dj1yr/Yaesu-Quadra-VL-1000-FAN-Controller/IMG_20241115_044554092.jpg

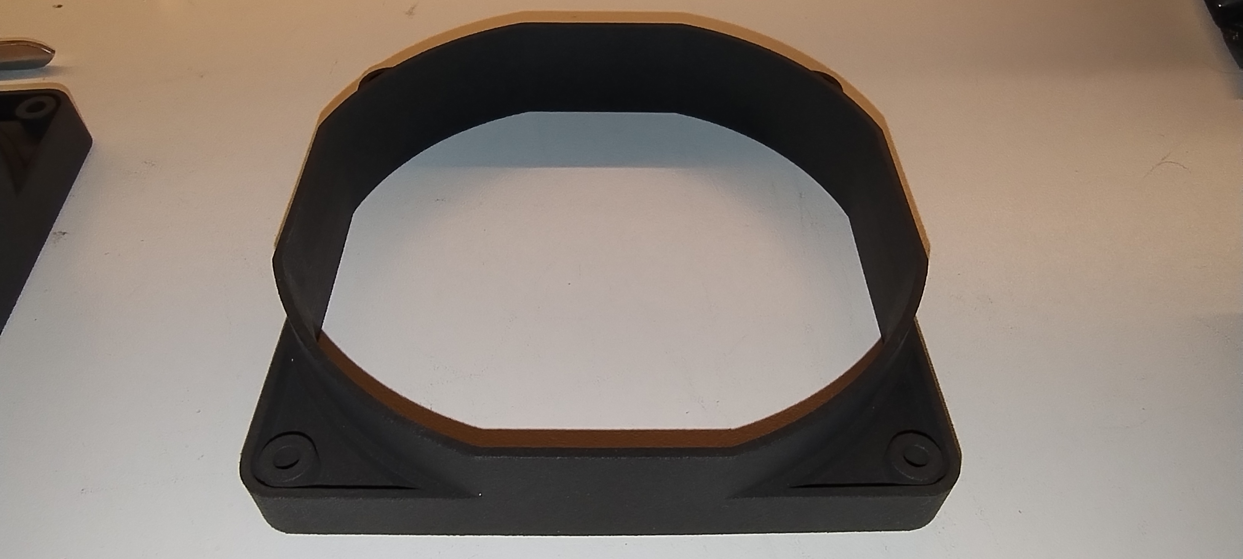
IMG_20241115_044554092.jpg
