dj1yr/Yaesu-Quadra-VL-1000-FAN-Controller/IMG_20241115_045349877.jpg

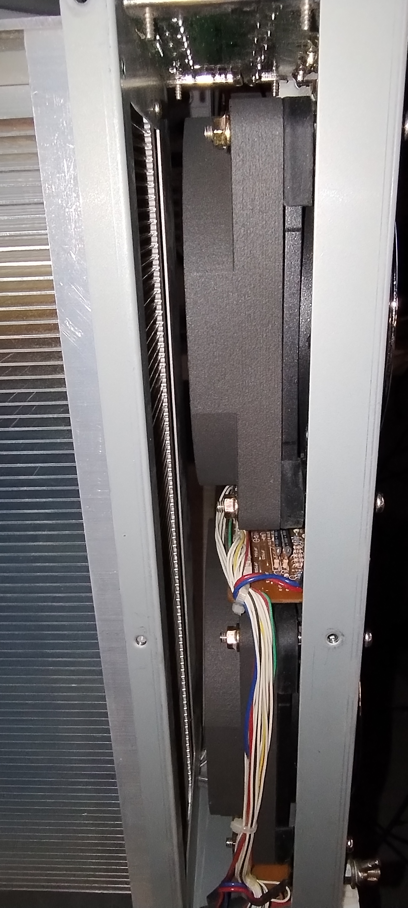
IMG_20241115_045349877.jpg
